Yurihou/EPaperNameBadge/ESP32Code/picdata.h

const unsigned char screenData[4736] = { /* 0X81,0X01,0X28,0X01,0X80,0X00, */
0XFF,0XFF,0XFF,0XFF,0XFF,0XFF,0XFF,0XFF,0XFF,0XFF,0XFF,0XFF,0XFF,0XFF,0XFF,0XFF,
0XFF,0XFF,0XFF,0XFF,0XFF,0XFF,0XFF,0XFF,0XFF,0XFF,0XFF,0XFF,0XFF,0XFF,0XFF,0XFF,
0XFF,0XFF,0XFF,0XFF,0XFC,0XFF,0XFF,0XFF,0XFF,0XFF,0XFF,0XFF,0XFF,0XFF,0XFF,0XFF,
0XFF,0XFF,0XFF,0XFF,0XFC,0XFF,0XFF,0XFF,0XFF,0XFF,0XFF,0XFF,0XFF,0XFF,0XFF,0XFF,
0XFF,0XFF,0XFF,0XFF,0XFC,0XFF,0XFF,0XFF,0XFF,0XFF,0XFF,0XFF,0XFF,0XFF,0XFF,0XFF,
0XFF,0XFF,0XFF,0XFF,0XFC,0XFF,0XFF,0XFF,0XFF,0XFF,0XFF,0XFF,0XFF,0XFF,0XFF,0XFF,
0XFF,0XFF,0XFF,0XFF,0XFC,0XFF,0XFF,0XFF,0XFF,0XFF,0XFF,0XFF,0XFF,0XFF,0XFF,0XFF,
0XFF,0XFF,0XFF,0XFF,0XFC,0XFF,0XFF,0XFF,0XFF,0XFF,0XFF,0XFF,0XFF,0XFF,0XFF,0XFF,
0XFF,0XFF,0XFF,0XFF,0XFC,0XFE,0X00,0X06,0X61,0XE0,0X60,0X66,0X61,0XE0,0X60,0X7F,
0XFF,0XFF,0XFF,0XFF,0XFC,0XFE,0X00,0X06,0X61,0XE0,0X60,0X66,0X61,0XE0,0X60,0X7F,
0XFF,0XFF,0XFF,0XFF,0XFC,0XFE,0X7F,0XE6,0X79,0XE1,0XE6,0X19,0XE6,0X67,0XFE,0X7F,
0XFF,0XFF,0XFF,0XFF,0XFC,0XFE,0X7F,0XE6,0X79,0XE1,0XE6,0X19,0XE6,0X67,0XFE,0X7F,
0XFF,0XFF,0XFF,0XFF,0XFC,0XFE,0X60,0X66,0X7E,0X1E,0X66,0X06,0X7E,0X7E,0X7E,0X7F,
0XFF,0XFC,0X00,0XFF,0XFC,0XFE,0X60,0X66,0X7E,0X1E,0X66,0X06,0X7E,0X7E,0X7E,0X7F,
0XFF,0XFC,0X00,0XFF,0XFC,0XFE,0X60,0X67,0XE1,0X87,0X9E,0X66,0X61,0XE7,0XF8,0X7F,
0XFF,0XFC,0XF9,0XFF,0XFC,0XFE,0X60,0X67,0XE1,0X87,0X9E,0X66,0X61,0XE7,0XF8,0X7F,
0XFF,0XFC,0XF9,0XFF,0XFC,0XFE,0X60,0X67,0X80,0X60,0X60,0X7F,0XF8,0X00,0X19,0XFF,
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
0XFF,0XFF,0XFF,0XFF,0XFF,0XFF,0XFF,0XFF,0XFF,0XFF,0XFF,0XFF,0XFF,0XFF,0XFF,0XFF,
0XFF,0XFF,0XFF,0XFF,0XFF,0XFF,0XFF,0XFF,0XFF,0XFF,0XFF,0XFF,0XFF,0XFF,0XFF,0XFF,
0XFF,0XFF,0XFF,0XFF,0XFF,0XFF,0XFF,0XFF,0XFF,0XFF,0XFF,0XFF,0XFF,0XFF,0XFF,0XFF,
0XFF,0XFF,0XFF,0XFF,0XFF,0XFF,0XFF,0XFF,0XFF,0XFF,0XFF,0XFF,0XFF,0XFF,0XFF,0XFF,
};
