Yurihou/EPaperNameBadge/ESP32Code/screen.h

#ifndef _SCREEN_H_
#define _SCREEN_H_

#include <SPI.h>

#define VSPI_MISO   MISO
#define VSPI_MOSI   MOSI
#define VSPI_SCLK   SCK
#define VSPI_SS     SS

#define DAT HIGH
#define CMD LOW

#define DC 21
#define RST 22
#define ISBUSY 17

static const int spiClk = 1000000; // 1 MHz

class eInkScreen
{
  SPIClass screen;
  int partialRefreshTime;

  // unsigned char screenData[4736] = {0};

  void sendByte(char dc, char data);
  
  void isScreenBusy();
  void screenInit();
  void screenWrite();
  void screenRefresh();
  void screenSleep();
  
public:
  eInkScreen();
  void screenGlobalChange();
  void screenPartialChange(int y1, int x1, int y2, int x2);
};

#endif
